tuxedomakes/mantaray-pro-wireless/pcb/mantaray_pro_wireless_panel_xiao.kicad_sch

## KiCad design pcb/mantaray_pro_wireless_panel_xiao.kicad_sch (2026-03-07)

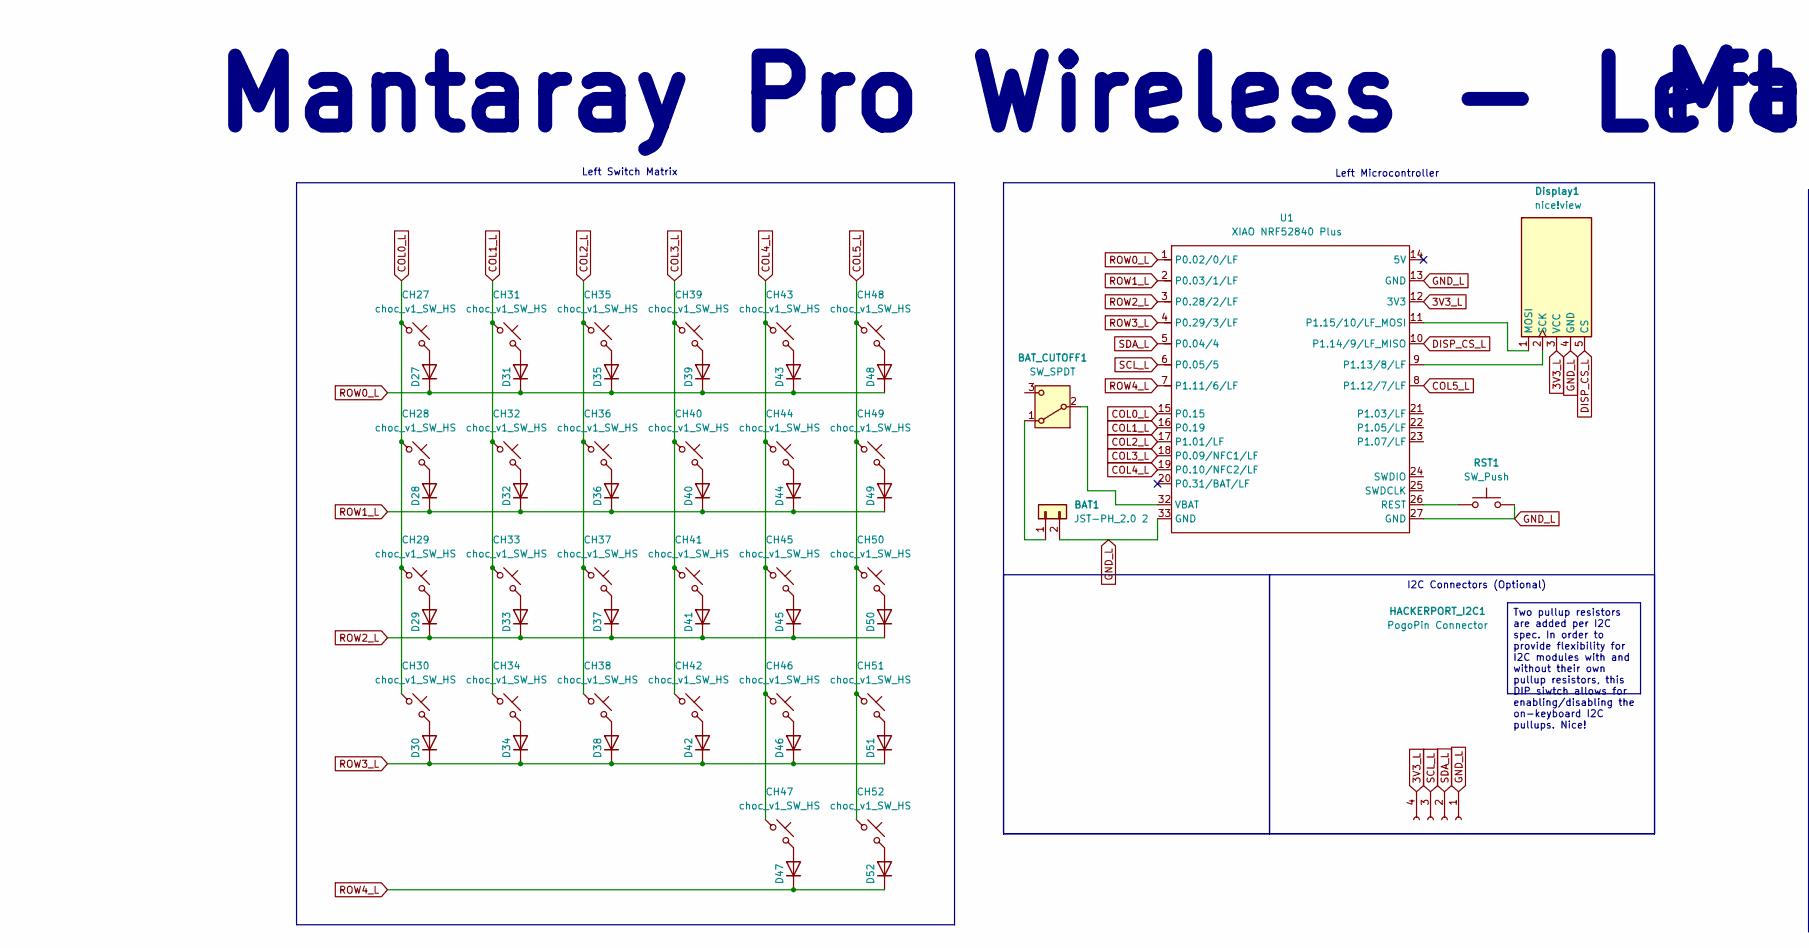
[picture p5: schematic mantaray_pro_wireless_panel_xiao.kicad_sch, part in row 1, column 1]

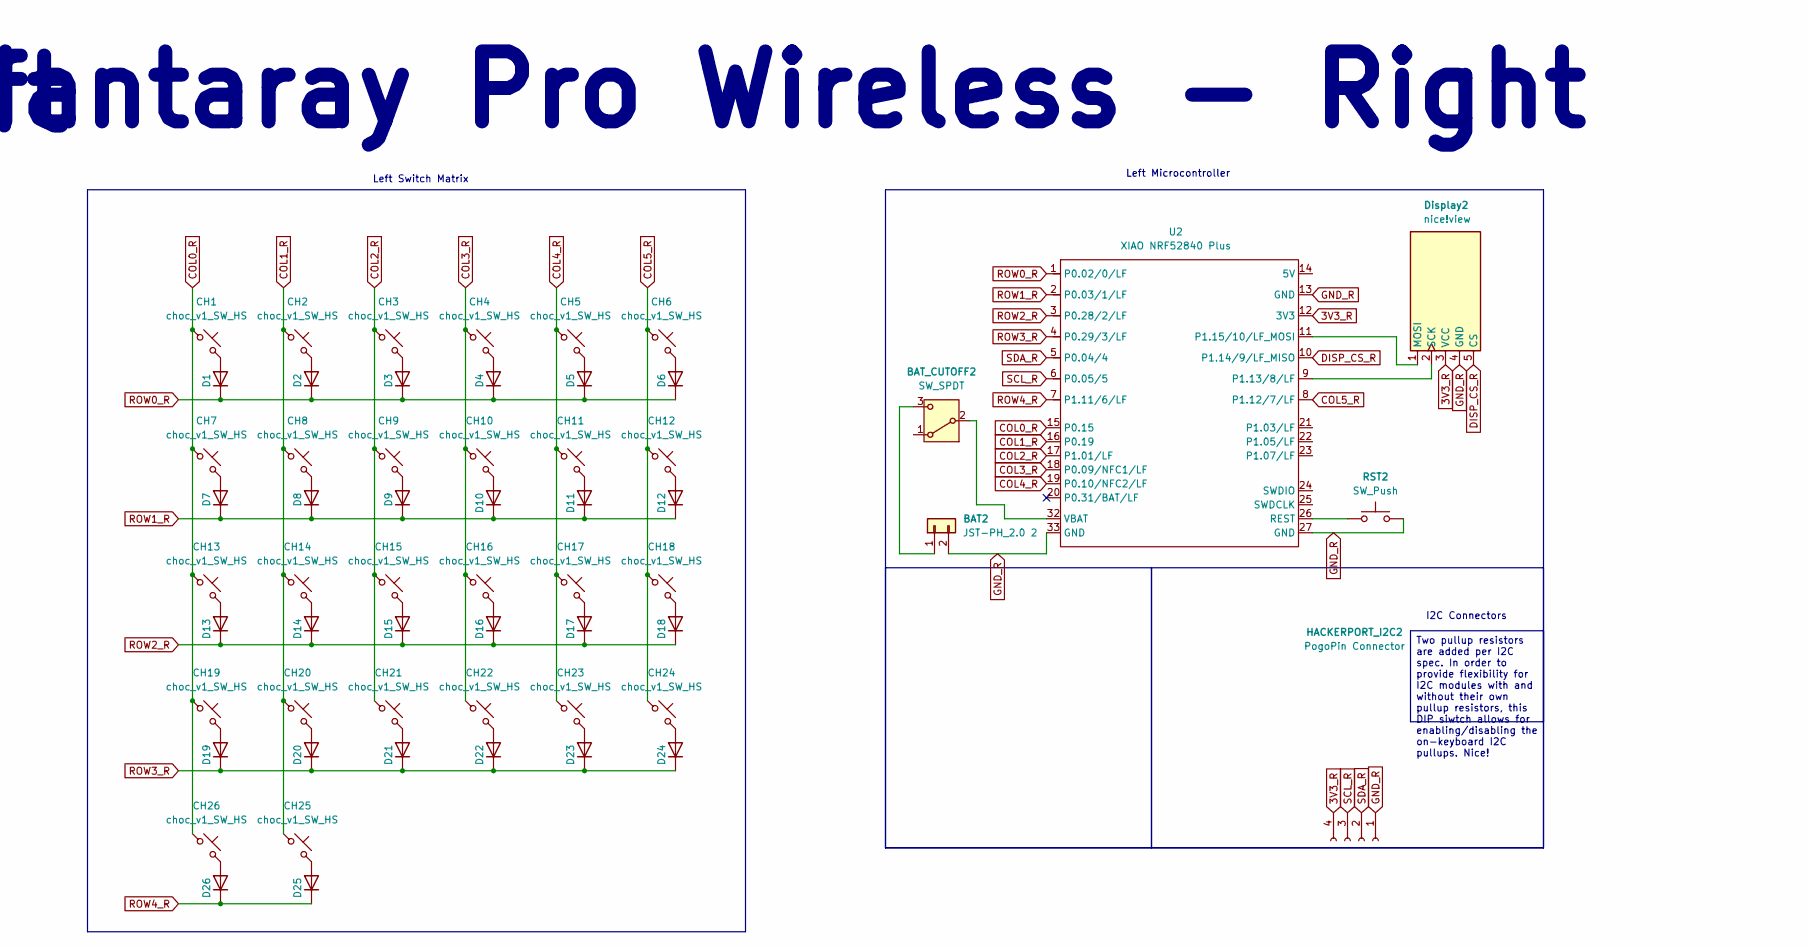
[picture p6: schematic mantaray_pro_wireless_panel_xiao.kicad_sch, part in row 1, column 2]

Parts:
BAT1, BAT2: JST-PH_2.0 2; JST_PH_S2B-PH-K_1x02_P2.00mm_Horizontal
BAT_CUTOFF1, BAT_CUTOFF2: SW_SPDT; SW_MSK12C02-HB; Part # MK-12C02-G025
CH1, CH2, CH3, CH4, CH5, CH6, CH7, CH8, CH9, CH10, CH11, CH12, CH13, CH14, CH15, CH16, CH17, CH18, CH19, CH20, CH21, CH22, CH23, CH24, CH25, CH26, CH27, CH28, CH29, CH30, CH31, CH32, CH33, CH34, CH35, CH36, CH37, CH38, CH39, CH40, CH41, CH42, CH43, CH44, CH45, CH46, CH47, CH48, CH49, CH50, CH51, CH52: choc_v1_SW_HS; SW_choc_v1_HS_CPG135001S30_1u_18x17_spacing
D1, D2, D3, D4, D5, D6, D7, D8, D9, D10, D11, D12, D13, D14, D15, D16, D17, D18, D19, D20, D21, D22, D23, D24, D25, D26, D27, D28, D29, D30, D31, D32, D33, D34, D35, D36, D37, D38, D39, D40, D41, D42, D43, D44, D45, D46, D47, D48, D49, D50, D51, D52: 1N4148W; D_SOD-123
Display1, Display2: nice!view; nice_view
HACKERPORT_I2C1, HACKERPORT_I2C2: PogoPin Connector; PogoPin_Female_4pin_2.54pitch
RST1, RST2: SW_Push; SW_SPST_SKQG_WithStem
U1, U2: XIAO NRF52840 Plus; seeed_xiao_nrf52840_plus_smd

Connections:
3V3_L: Display1.3 (VCC), HACKERPORT_I2C1.4, U1.12 (3V3)
3V3_R: Display2.3 (VCC), HACKERPORT_I2C2.4, U2.12 (3V3)
COL0_L: CH27.1, CH28.1, CH29.1, CH30.1, U1.15 (P0.15)
COL0_R: CH1.1, CH7.1, CH13.1, CH19.1, CH26.1, U2.15 (P0.15)
COL1_L: CH31.1, CH32.1, CH33.1, CH34.1, U1.16 (P0.19)
COL1_R: CH2.1, CH8.1, CH14.1, CH20.1, CH25.1, U2.16 (P0.19)
COL2_L: CH35.1, CH36.1, CH37.1, CH38.1, U1.17 (P1.01/LF)
COL2_R: CH3.1, CH9.1, CH15.1, CH21.1, U2.17 (P1.01/LF)
COL3_L: CH39.1, CH40.1, CH41.1, CH42.1, U1.18 (P0.09/NFC1/LF)
COL3_R: CH4.1, CH10.1, CH16.1, CH22.1, U2.18 (P0.09/NFC1/LF)
COL4_L: CH43.1, CH44.1, CH45.1, CH46.1, CH47.1, U1.19 (P0.10/NFC2/LF)
COL4_R: CH5.1, CH11.1, CH17.1, CH23.1, U2.19 (P0.10/NFC2/LF)
COL5_L: CH48.1, CH49.1, CH50.1, CH51.1, CH52.1, U1.8 (P1.12/7/LF)
COL5_R: CH6.1, CH12.1, CH18.1, CH24.1, U2.8 (P1.12/7/LF)
DISP_CS_L: Display1.5 (CS), U1.10 (P1.14/9/LF_MISO)
DISP_CS_R: Display2.5 (CS), U2.10 (P1.14/9/LF_MISO)
GND_L: BAT1.2 (B-), Display1.4 (GND), HACKERPORT_I2C1.1, RST1.2, U1.13 (GND), U1.27 (GND), U1.33 (GND)
GND_R: BAT2.2 (B-), Display2.4 (GND), HACKERPORT_I2C2.1, RST2.2, U2.13 (GND), U2.27 (GND), U2.33 (GND)
unnamed: BAT1.1 (B+), BAT_CUTOFF1.1 (A)
unnamed: BAT2.1 (B+), BAT_CUTOFF2.3 (C)
unnamed: BAT_CUTOFF1.2 (B), U1.32 (VBAT)
unnamed: BAT_CUTOFF2.2 (B), U2.32 (VBAT)
unnamed: CH1.2, D1.2 (A)
unnamed: CH2.2, D2.2 (A)
unnamed: CH3.2, D3.2 (A)
unnamed: CH4.2, D4.2 (A)
unnamed: CH5.2, D5.2 (A)
unnamed: CH6.2, D6.2 (A)
unnamed: CH7.2, D7.2 (A)
unnamed: CH8.2, D8.2 (A)
unnamed: CH9.2, D9.2 (A)
unnamed: CH10.2, D10.2 (A)
unnamed: CH11.2, D11.2 (A)
unnamed: CH12.2, D12.2 (A)
unnamed: CH13.2, D13.2 (A)
unnamed: CH14.2, D14.2 (A)
unnamed: CH15.2, D15.2 (A)
unnamed: CH16.2, D16.2 (A)
unnamed: CH17.2, D17.2 (A)
unnamed: CH18.2, D18.2 (A)
unnamed: CH19.2, D19.2 (A)
unnamed: CH20.2, D20.2 (A)
unnamed: CH21.2, D21.2 (A)
unnamed: CH22.2, D22.2 (A)
unnamed: CH23.2, D23.2 (A)
unnamed: CH24.2, D24.2 (A)
unnamed: CH25.2, D25.2 (A)
unnamed: CH26.2, D26.2 (A)
unnamed: CH27.2, D27.2 (A)
unnamed: CH28.2, D28.2 (A)
unnamed: CH29.2, D29.2 (A)
unnamed: CH30.2, D30.2 (A)
unnamed: CH31.2, D31.2 (A)
unnamed: CH32.2, D32.2 (A)
unnamed: CH33.2, D33.2 (A)
unnamed: CH34.2, D34.2 (A)
unnamed: CH35.2, D35.2 (A)
unnamed: CH36.2, D36.2 (A)
unnamed: CH37.2, D37.2 (A)
unnamed: CH38.2, D38.2 (A)
unnamed: CH39.2, D39.2 (A)
unnamed: CH40.2, D40.2 (A)
unnamed: CH41.2, D41.2 (A)
unnamed: CH42.2, D42.2 (A)
unnamed: CH43.2, D43.2 (A)
unnamed: CH44.2, D44.2 (A)
unnamed: CH45.2, D45.2 (A)
unnamed: CH46.2, D46.2 (A)
unnamed: CH47.2, D47.2 (A)
unnamed: CH48.2, D48.2 (A)
unnamed: CH49.2, D49.2 (A)
unnamed: CH50.2, D50.2 (A)
unnamed: CH51.2, D51.2 (A)
unnamed: CH52.2, D52.2 (A)
unnamed: Display1.1 (MOSI), U1.11 (P1.15/10/LF_MOSI)
unnamed: Display1.2 (SCK), U1.9 (P1.13/8/LF)
unnamed: Display2.1 (MOSI), U2.11 (P1.15/10/LF_MOSI)
unnamed: Display2.2 (SCK), U2.9 (P1.13/8/LF)
unnamed: RST1.1, U1.26 (REST)
unnamed: RST2.1, U2.26 (REST)
ROW0_L: D27.1 (K), D31.1 (K), D35.1 (K), D39.1 (K), D43.1 (K), D48.1 (K), U1.1 (P0.02/0/LF)
ROW0_R: D1.1 (K), D2.1 (K), D3.1 (K), D4.1 (K), D5.1 (K), D6.1 (K), U2.1 (P0.02/0/LF)
ROW1_L: D28.1 (K), D32.1 (K), D36.1 (K), D40.1 (K), D44.1 (K), D49.1 (K), U1.2 (P0.03/1/LF)
ROW1_R: D7.1 (K), D8.1 (K), D9.1 (K), D10.1 (K), D11.1 (K), D12.1 (K), U2.2 (P0.03/1/LF)
ROW2_L: D29.1 (K), D33.1 (K), D37.1 (K), D41.1 (K), D45.1 (K), D50.1 (K), U1.3 (P0.28/2/LF)
ROW2_R: D13.1 (K), D14.1 (K), D15.1 (K), D16.1 (K), D17.1 (K), D18.1 (K), U2.3 (P0.28/2/LF)
ROW3_L: D30.1 (K), D34.1 (K), D38.1 (K), D42.1 (K), D46.1 (K), D51.1 (K), U1.4 (P0.29/3/LF)
ROW3_R: D19.1 (K), D20.1 (K), D21.1 (K), D22.1 (K), D23.1 (K), D24.1 (K), U2.4 (P0.29/3/LF)
ROW4_L: D47.1 (K), D52.1 (K), U1.7 (P1.11/6/LF)
ROW4_R: D25.1 (K), D26.1 (K), U2.7 (P1.11/6/LF)
SCL_L: HACKERPORT_I2C1.3, U1.6 (P0.05/5)
SCL_R: HACKERPORT_I2C2.3, U2.6 (P0.05/5)
SDA_L: HACKERPORT_I2C1.2, U1.5 (P0.04/4)
SDA_R: HACKERPORT_I2C2.2, U2.5 (P0.04/4)

Notes on the sheet:
Left Microcontroller
I2C Connectors
Left Switch Matrix
Mantaray Pro Wireless - Left
I2C Connectors (Optional)
Mantaray Pro Wireless - Right
Two pullup resistors are added per I2C spec. In order to provide flexibility for I2C modules with and without their own pullup resistors, this DIP siwtch allows for enabling/disabling the on-keyboard I2C pullups. Nice!
